socrateJrr/InkTime/Images/all2.png

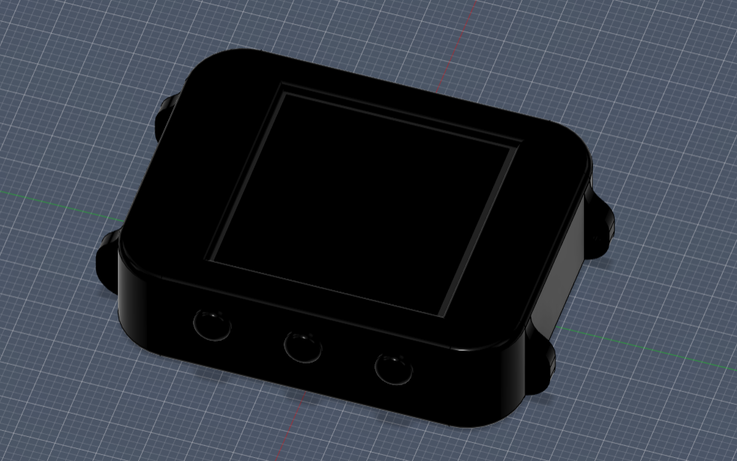
Images/all2.png
